rkolbi/voron2.4/DK-TAP-SENSORLESS-EBB36-CPAP-BEDFANS/ACTIVE/MACRO-PRINT_HANDLING.cfg

#.................................................................................................................
[gcode_macro _PRINT_VARIABLES]
variable_extruder_temp: 235
variable_extruder_temp2: 235
variable_extruder_warm: 160
variable_fpline: 37.5
variable_spline: 75.0   
variable_swap_executed: 0
variable_pause_on_layer_change: 0
gcode:
    M117 Happy Printing



#.................................................................................................................
[gcode_macro PRINT_START]
description: Performs all needed moves prior to printing
gcode:
    CLEAR_PAUSE                                            ; Clear pause state from previous print
    BED_MESH_CLEAR                                         ; Clear bed mesh data from the previous print
    M220 S100                                              ; Reset feedrate to 100%
    M221 S100                                              ; Reset flowrate to 100%
	
    # Bring in variables passed by the slicer. If needed variables are not passed then PRINT_START will use default values set in the printer.cfg file. 

    # SuperSlicer 'Start G-Code' example follows:
    # M104 S0 ; Stops PS/SS from sending temp waits separately
    # M140 S0
    # PRINT_START BED_TEMP=[first_layer_bed_temperature] EXTRUDER_TEMP=[first_layer_temperature] EXTRUDER_TEMP2=[temperature] CHAMBER_TEMP=[chamber_temperature] SOAK=15 PA=0.045 ST=0.21 SIZE={first_layer_print_min[0]}_{first_layer_print_min[1]}_{first_layer_print_max[0]}_{first_layer_print_max[1]}

    # PrusaSlicer 'Start G-Code' example follows (have to hard-write chamber temp):
    # M104 S0 ; Stops PS/SS from sending temp waits separately
    # M140 S0
    # PRINT_START BED_TEMP=[first_layer_bed_temperature] EXTRUDER_TEMP=[first_layer_temperature] EXTRUDER_TEMP2=[temperature] CHAMBER_TEMP=50 SOAK=15 PA=0.045 ST=0.21 SIZE={first_layer_print_min[0]}_{first_layer_print_min[1]}_{first_layer_print_max[0]}_{first_layer_print_max[1]}
    
    {% set FL_SIZE = params.SIZE|default("0_0_0_0")|string %}                                                               ; Get mesh parameters from slicer
    COMPUTE_MESH_PARAMETERS SIZE={FL_SIZE}                                                                                  ; Compute mesh parameters
    {% set PA = params.PA|default(printer.configfile.config['extruder']['pressure_advance'])|float %}                       ; Set pressure advance
    {% set ST = params.ST|default(printer.configfile.config['extruder']['pressure_advance_smooth_time'])|float %}           ; Set pressure advance
    {% set EXTRUDER_TEMP = params.EXTRUDER_TEMP|default(printer['gcode_macro globalvariables'].defaulttempnozzle)|float %}  ; Set first-layer extruder temperature
    {% set EXTRUDER_TEMP2 = params.EXTRUDER_TEMP2|default(EXTRUDER_TEMP)|float %}                                           ; Set extruder temperature
    {% set EXTRUDER_WARM = params.EXTRUDER_WARM|default(printer["gcode_macro globalvariables"].defaultwarmnozzle)|float %}  ; Set extruder warm temperature
    {% set SOAK = params.SOAK|default(printer["gcode_macro globalvariables"].preprintsoakminutes)|float %}                  ; Set pre-print soak time
    {% set BED_TEMP = params.BED_TEMP|default(printer["gcode_macro globalvariables"].defaulttempbed)|float %}               ; Set bed temperature
    {% set fpline = params.fpline|default(printer['gcode_macro globalvariables'].fpline)|float %}                           ; Get E value for first 120mm prime line, implemented as (fpline * NZLD)
    {% set spline = params.spline|default(printer['gcode_macro globalvariables'].spline)|float %}                           ; Get E value for second 120mm prime line, implemented as (spline * NZLD)
    {% set CHAMBER_TEMP = params.CHAMBER_TEMP|default(printer["gcode_macro globalvariables"].bedfanchambertemp)|float %}    ; Set chamber temperature
    SET_PRESSURE_ADVANCE ADVANCE={PA} SMOOTH_TIME={ST}                                                                      ; Set pressure advance
    SET_GCODE_VARIABLE MACRO=_PRINT_VARIABLES VARIABLE=extruder_temp VALUE={EXTRUDER_TEMP}                                  ; Set first-layer extruder temperature
    SET_GCODE_VARIABLE MACRO=_PRINT_VARIABLES VARIABLE=extruder_temp2 VALUE={EXTRUDER_TEMP2}                                ; Set extruder temperature
    SET_GCODE_VARIABLE MACRO=_PRINT_VARIABLES VARIABLE=extruder_warm VALUE={EXTRUDER_WARM}                                  ; Set extruder warm temperature
    SET_GCODE_VARIABLE MACRO=_PRINT_VARIABLES VARIABLE=swap_executed VALUE=0                                                ; Set swap flag to off
    SET_GCODE_VARIABLE MACRO=_PRINT_VARIABLES VARIABLE=pause_on_layer_change VALUE=0                                        ; Set layer change pause flag to off
    SET_GCODE_VARIABLE MACRO=_PRINT_VARIABLES VARIABLE=fpline VALUE={fpline}                                                ; Set first 120mm prime line, implemented as (fpline * NZLD)
    SET_GCODE_VARIABLE MACRO=_PRINT_VARIABLES VARIABLE=spline VALUE={spline}                                                ; Set second 120mm prime line, implemented as (spline * NZLD)
    SET_GCODE_VARIABLE MACRO=_BEDFANVARS VARIABLE=bedfanchambertarget VALUE={CHAMBER_TEMP}

    ; Override MACRO-BED_FANS variables with those from printer.cfg
    {% set bedfantripon = printer["gcode_macro globalvariables"].bedfantripon|float %}
    {% set bedfanmin = printer["gcode_macro globalvariables"].bedfanmin|float %}
    {% set bedfanmax = printer["gcode_macro globalvariables"].bedfanmax|float %}
    {% set bedfannormal = printer["gcode_macro globalvariables"].bedfannormal|float %}
    SET_GCODE_VARIABLE MACRO=_BEDFANVARS VARIABLE=bedfantripon VALUE={bedfantripon}
    SET_GCODE_VARIABLE MACRO=_BEDFANVARS VARIABLE=bedfanmin VALUE={bedfanmin}
    SET_GCODE_VARIABLE MACRO=_BEDFANVARS VARIABLE=bedfanmax VALUE={bedfanmax}
    SET_GCODE_VARIABLE MACRO=_BEDFANVARS VARIABLE=bedfannormal VALUE={bedfannormal}

    M118 {rawparams}                                       ; Display all passed parameters
    M118 gCode file passed the following to PRINT_START:   ; Display message on LCD screen

    M118 PA: {PA}
    M118 ST: {ST}
    M118 fpline: {fpline}
    M118 spline: {spline}
    M118 EXTRUDER, FIRST LAYER TEMP: {EXTRUDER_TEMP}
    M118 EXTRUDER, REST OF PRINT TEMP: {EXTRUDER_TEMP2}
    M118 EXTRUDER, WARM TEMP: {EXTRUDER_WARM}
    M118 SOAK: {SOAK}
    M118 BED TEMP: {BED_TEMP}
    M118 CHAMBER TEMP: {CHAMBER_TEMP}
    M118 Following parameters are set to prepare print:    ; Display message on LCD screen

    M140 S{BED_TEMP}                                       ; Set bed temperature
    G90                                                    ; Absolute positioning
    G21                                                    ; Millimeters
    M83                                                    ; Extruder relative mode
    G92 E0.0                                               ; Reset the extruder position
    SET_GCODE_OFFSET Z=0.0                                 ; Reset the G-Code Z offset
    M117 Performing initial homing.                        ; Display message on LCD screen
    BED_MESH_CLEAR                                         ; Clear bed mesh data from the previous print
    G28                                                    ; Home all axes
    M117 Performing initial QGL.                           ; Display message on LCD screen
    QUAD_GANTRY_LEVEL                                      ; Perform QGL
    G28 Z                                                  ; Home Z axis
    SET_HEATER_TEMPERATURE HEATER=extruder TARGET=0        ; Ensure hotend heater is off
    PARK_Center                                            ; Park the nozzle at the center of the bed
    M117 Bringing bed to temperature.                      ; Display message on LCD screen
    STATUS_HEATING                                         ; Set status to heating
    SET_NOZZLE_LEDS_ON                                     ; Turn on nozzle LEDs

    M190 S{BED_TEMP}                                       ; Wait for the bed to reach temperature

    {% if params.NONPRINT %}                               ; If NONPRINT is passed then need to use the blocking wait routine
        _HEAT_WAIT MINUTES={SOAK}                          ; Wait for SOAK minutes
        _PRINT_START2                                      ; Start sudo print
      {% else %}                                           ; If NONPRINT is not passed then continue and use the non-blocking wait routine
        _WAIT_Start MINUTES={SOAK}                         ; Wait for SOAK minutes
    {% endif %}                                            ; End if statement


#.................................................................................................................
[gcode_macro _PRINT_START2]
description: Part 2 - Performs all needed moves prior to printing
gcode:
    RESUME_BASE                                            ; Resume print
    {% set EXTRUDER_WARM = printer["gcode_macro _PRINT_VARIABLES"].extruder_warm|int %}   ; Get extruder warm temperature
    {% set EXTRUDER_TEMP = printer["gcode_macro _PRINT_VARIABLES"].extruder_temp|int %}   ; Get first-layer extruder temperature
    {% set EXTRUDER_TEMP2 = printer["gcode_macro _PRINT_VARIABLES"].extruder_temp2|int %} ; Get extruder temperature
    M104 S{EXTRUDER_WARM}                                  ; Set extruder temperature
    M117 Warming nozzle for hot level.                     ; Display message on LCD screen
    TEMPERATURE_WAIT SENSOR=extruder MINIMUM={EXTRUDER_WARM} MAXIMUM={EXTRUDER_WARM + 3}  ; Wait for extruder warm temp within 3 degrees
    CURRENT_HIGH                                           ; Set current to high
    M117 Performing hot level.                             ; Display message on LCD screen
    M400                                                   ; Wait for moves to complete
    G3201                                                  ; Perform hot level and mesh
    M104 S{EXTRUDER_TEMP}                                  ; Set first-layer extruder temperature
    M117 Moving nozzle to purgle line start position.      ; Display message on LCD screen
    G1 X0 Y20 F4000                                        ; Move nozzle to side
    G1 Z1.5                                                ; Move nozzle to over bed
    M400                                                   ; Wait for moves to finish
    STATUS_HEATING                                         ; Set status to heating
    SET_NOZZLE_LEDS_ON                                     ; Turn on nozzle LEDs
    M117 Bringing nozzle to temperature.                   ; Display message on LCD screen
    M118 Bringing nozzle to temperature.                   ; Display message on LCD screen
    TEMPERATURE_WAIT SENSOR=extruder MINIMUM={EXTRUDER_TEMP} MAXIMUM={EXTRUDER_TEMP + 3}  ; Wait for extruder temp within 3 degrees
    _FILAMENT_READY                                        ; Perform filament purge line and readies for print
    M117 Printing.                                         ; Display message on LCD screen
    M118 Printing.                                         ; Display message on LCD screen
    STATUS_PRINTING                                        ; Set status to printing
    M400
    SET_NOZZLE_LEDS_ON                                     ; Turn on nozzle LEDs


#.................................................................................................................	
[gcode_macro _FILAMENT_READY]
description: Performs filament specific purge line and readies for print
gcode:
    STATUS_BUSY                                            ; Set status to busy
    SET_NOZZLE_LEDS_ON                                     ; Turn on nozzle LEDs
    SET_VELOCITY_LIMIT ACCEL={printer["gcode_macro globalvariables"].limitaccel|float} ACCEL_TO_DECEL={printer["gcode_macro globalvariables"].limitdecel|float} ; Set velocity limits
    {% set NZLD = printer.configfile.config["extruder"]["nozzle_diameter"]|float %}                                                                             ; Get nozzle diameter from config
    {% set purgeRetract = printer["gcode_macro globalvariables"].purgeretract|float %}                                                                          ; Get retraction for purge line from config
    {% set X_MeshCenter, Y_MeshCenter = printer["gcode_macro _ADAPTIVE_MESH_VARIABLES"].mesh_center.split(',')|map('trim')|map('int') %}                        ; Get mesh center
    {% set EXTRUDER_TEMP = printer["gcode_macro _PRINT_VARIABLES"].extruder_temp|int %}                                                                         ; Get first-layer extruder temperature
    {% set EXTRUDER_TEMP2 = printer["gcode_macro _PRINT_VARIABLES"].extruder_temp2|int %}                                                                       ; Get extruder temperature
    {% set fpline = printer["gcode_macro _PRINT_VARIABLES"].fpline|float %}                                                                                     ; Get E value for first 120mm prime line
    {% set spline = printer["gcode_macro _PRINT_VARIABLES"].spline|float %}                                                                                     ; Get E value for second 120mm prime line

    {% set E20 = ( (0.1147475 * NZLD) * 20) |float %}      ; Calculate E value for 20mm line
    {% set E40 = ( (0.1147475 * NZLD) * 40) |float %}      ; Calculate E value for 40mm line

    M117 Purging nozzle.                                   ; Display message on LCD screen
    G1 X0 Y19.8 Z3 F300.0                                  ; Move nozzle
    M400                                                   ; Wait for moves to complete
    G1 X130 Y4.0 Z0.3 F3000.0                              ; Move nozzle to start position
    G1 X010 Y4.0 Z0.3 F1500.0 E{(fpline * NZLD)}           ; Extrude filament
    G1 X010 Y4.3 Z0.3 F5000.0                              ; Move nozzle
    M104 S{EXTRUDER_TEMP2}                                 ; Set extruder temperature
    G1 X130 Y4.3 Z0.3 F1500.0 E{(spline * NZLD)}           ; Extrude filament
    M400                                                   ; Wait for moves to complete

        ; Pressure advance verification line check
        M117 Printing PA test line at {EXTRUDER_TEMP2}C    ; Display message on LCD screen
        G1 Z0.25 F300                                      ; Move to layer height
        G1 X150 Y4.3 E{E20} F300                           ; Print line part one
        G1 X190 Y4.3 E{E40} F9000                          ; Print line part two
        G1 X210 Y4.3 E{E20} F300                           ; Print line part three
        M400                                               ; Wait for moves to complete
        ; End of Pressure advance verification line check

    M117 Increasing extruder to {EXTRUDER_TEMP}C for 1st layer  ; Display message on LCD screen
    M104 S{EXTRUDER_TEMP}                                  ; Set for first-layer extruder temperature
                                                           ; Can swap M104 with M109 to wait for temperature if hotend is slower
    G1 E-{purgeRetract} F3000                              ; Retract filament   
    G92 E0.0                                               ; Reset the extruder position
    G1 Z3 F3000                                            ; Move nozzle up
    M400                                                   ; Wait for moves to complete
    G1 X{X_MeshCenter} Y{Y_MeshCenter} F4000               ; Move nozzle to center of mesh
    G92 E0                                                 ; Reset extruder position
    M400                                                   ; Wait for moves to complete



#.................................................................................................................
[gcode_macro PRINT_END]
description: Performs all needed actions upon completion of printing
gcode:
    {% set EndRetract = printer["gcode_macro globalvariables"].endretract|float %}                                                              ; Get end of print retraction distance
    {% set EXTRUDER_WARM = printer["gcode_macro _PRINT_VARIABLES"].extruder_warm|int %}                                                         ; Get warm nozzle temperature
    SET_VELOCITY_LIMIT ACCEL={printer["gcode_macro globalvariables"].nplimitaccel|float} ACCEL_TO_DECEL={printer["gcode_macro globalvariables"].nplimitdecel|float} ; Set velocity limits
    SET_GCODE_VARIABLE MACRO=_ADAPTIVE_MESH_VARIABLES VARIABLE=mesh_center VALUE='"0,0"'                                                        ; Reset mesh center
    SET_GCODE_VARIABLE MACRO=_PRINT_VARIABLES VARIABLE=extruder_temp VALUE={printer["gcode_macro globalvariables"].defaulttempnozzle|float}     ; Reset extruder temperature
    SET_GCODE_VARIABLE MACRO=_PRINT_VARIABLES VARIABLE=extruder_warm VALUE={printer["gcode_macro globalvariables"].defaultwarmnozzle|float}     ; Reset warm nozzle temperature
    SET_GCODE_VARIABLE MACRO=_PRINT_VARIABLES VARIABLE=swap_executed VALUE=0                                                                    ; Set swap flag to off

    G91                                                    ; Relative positioning
    G0 Z5 F1000                                            ; Raise Z by 5mm
    G90                                                    ; Absolute positioning
    M220 S100                                              ; Reset speed to 100%
    M221 S100                                              ; Reset flow to 100%
    G92 E0                                                 ; Reset the extruder position
    G1 E-{EndRetract} F3600                                ; Retract filament
    M400                                                   ; Wait for moves to complete
    SAVE_GCODE_STATE NAME=STATE_PRINT_END                  ; Save current state   
    M400                                                   ; Wait for moves to complete
    BEDFANSOFF                                             ; Turn off bed fans
    TURN_OFF_HEATERS                                       ; Turn off heaters
    CURRENT_NORMAL                                         ; Set current to normal
    _COOL_WAIT MINUTES={printer["gcode_macro globalvariables"].postprintcool|float} NZL_TEMP={EXTRUDER_WARM} ; Wait for cool minutes
    PARK_UpperRight                                        ; Park the nozzle at the upper right of the bed
    M18 X Y E                                              ; Disable all steppers
    BED_MESH_CLEAR                                         ; Clear bed mesh data from the previous print
    RESTORE_GCODE_STATE NAME=STATE_PRINT_END               ; Restore saved state
    _COOL_WAIT MINUTES={printer["gcode_macro globalvariables"].postprintparkcool|float} NZL_TEMP=80 ; Wait for cool minutes until NZL 80c

    STOP_LED_EFFECTS                                       ; Turn off LED effects
    SET_LED LED=sb_leds RED=.3 GREEN=.5 BLUE=.4            ; Set LED to green
    M117 Finished printing, check nozzle clear.            ; Display message on LCD screen
    M118 Finished printing, check nozzle clear.            ; Display message on the terminal



#.................................................................................................................
[gcode_macro CANCEL_PRINT]
description: Cancel the actual running print
rename_existing: CANCEL_PRINT_BASE
gcode:
    {% if printer["gcode_macro _WAIT_Variable"].waiting %}          ; If waiting for user input
        WAIT_Quit                                                   ; Quit waiting
    {% else %}
    {% set EndRetract = printer["gcode_macro globalvariables"].endretract|float %}                                                              ; Get end of print retraction distance
    SET_VELOCITY_LIMIT ACCEL={printer["gcode_macro globalvariables"].nplimitaccel|float} ACCEL_TO_DECEL={printer["gcode_macro globalvariables"].nplimitdecel|float} ; Set velocity limits
    SET_GCODE_VARIABLE MACRO=_ADAPTIVE_MESH_VARIABLES VARIABLE=mesh_center VALUE='"0,0"'                                                        ; Reset mesh center
    SET_GCODE_VARIABLE MACRO=_PRINT_VARIABLES VARIABLE=extruder_temp VALUE={printer["gcode_macro globalvariables"].defaulttempnozzle|float}     ; Reset extruder temperature
    SET_GCODE_VARIABLE MACRO=_PRINT_VARIABLES VARIABLE=extruder_warm VALUE={printer["gcode_macro globalvariables"].defaultwarmnozzle|float}     ; Reset warm nozzle temperature
    SET_GCODE_VARIABLE MACRO=_PRINT_VARIABLES VARIABLE=swap_executed VALUE=0                                                                    ; Set swap flag to off
    SAVE_GCODE_STATE NAME=STATE_PRINT_END                  ; Save current state
    M400                                                   ; Wait for moves to complete
    M220 S100                                              ; Reset speed to 100%
    M221 S100                                              ; Reset flow to 100%
    G92 E0                                                 ; Reset the extruder position
    {% if printer.extruder.can_extrude|lower == 'true' %}  ; If extruder can extrude
        G1 E-{EndRetract} F3600                            ; Retract filament
    {% endif %}                                            ; End if extruder check
    CLEAR_PAUSE                                            ; Clear pause state
    BEDFANSOFF                                             ; Turn off bed fans
    TURN_OFF_HEATERS                                       ; Turn off heaters
    CANCEL_PRINT_BASE                                      ; Call original macro
    CURRENT_NORMAL                                         ; Set current to normal
    M106 S250                                              ; Turn on the fan
    G90                                                    ; Absolute positioning
    PARK_UpperRight                                        ; Park the nozzle at the upper right of the bed
    M18 X Y E                                              ; Disable all steppers
    BED_MESH_CLEAR                                         ; Clear bed mesh data from the previous print
    RESTORE_GCODE_STATE NAME=STATE_PRINT_END               ; Restore saved state
    _COOL_WAIT MINUTES={printer["gcode_macro globalvariables"].postprintparkcool|float} NZL_TEMP=80 ; Wait for cool minutes until NZL 80c

    M117 Cancelled print, check nozzle clear.              ; Display message on LCD screen
    M118 Cancelled print, check nozzle clear.              ; Display message on the terminal
    STATUS_READY                                           ; Set status to ready
    {% endif %} 


#.................................................................................................................
[gcode_macro PAUSE]
description: Pause the actual running print
rename_existing: PAUSE_BASE
gcode:
    {% set X_MID = printer.configfile.config["stepper_x"]["position_max"]|float / 2.0 %} ; Get X midpoint
    SET_GCODE_VARIABLE MACRO=_PRINT_VARIABLES VARIABLE=extruder_temp VALUE="{printer[printer.toolhead.extruder].target}"  ; Save current extruder temperature
    {% set x = params.X|default(X_MID) %}                   ; X position to move to
    {% set y = params.Y|default(20) %}                      ; Y position to move to
    {% set z = params.Z|default(10)|float %}                ; Z position to move to
    {% set e = params.E|default(1) %}                       ; E position to move to
    {% set max_z = printer.toolhead.axis_maximum.z|float %} ; Maximum Z position
    {% set act_z = printer.toolhead.position.z|float %}     ; Actual Z position
    {% set lift_z = z|abs %}                                ; Z lift distance
    {% if act_z < (max_z - lift_z) %}                       ; Check if Z is high enough
        {% set z_safe = lift_z %}                           ; Set Z lift distance
      {% else %}                                            ; If not high enough
        {% set z_safe = max_z - act_z %}                    ; Set Z lift distance to maximum
    {% endif %}                                             ; End if Z is high enough
    PAUSE_BASE                                              ; Call original macro
    G91                                                     ; Relative positioning
    {% if printer.extruder.can_extrude|lower == 'true' %}   ; If extruder can extrude
        G1 E-{e} F2100                                      ; Retract filament
      {% else %}                                            ; If extruder can't extrude
        {action_respond_info("Extruder not hot enough")}    ; Display message on terminal
    {% endif %}                                             ; End if extruder can extrude
    {% if "xyz" in printer.toolhead.homed_axes %}           ; If printer is homed
        G1 Z{z_safe}                                        ; Lift Z
        G90                                                 ; Absolute positioning
        G1 X{x} Y{y} F4000                                  ; Move to X Y
      {% else %}                                            ; If printer is not homed
        {action_respond_info("Printer not homed")}          ; Display message on terminal
    {% endif %}                                             ; End if printer is homed



#.................................................................................................................
[gcode_macro M600]
description: Call to pause
gcode:
    SET_GCODE_VARIABLE MACRO=_PRINT_VARIABLES VARIABLE=extruder_temp VALUE="{printer[printer.toolhead.extruder].target}"  ; Save current extruder temperature
    SAVE_GCODE_STATE NAME=M600_state                      ; Save current state
    SET_GCODE_VARIABLE MACRO=_PRINT_VARIABLES VARIABLE=swap_executed VALUE=1  ; Set swap flag to on
    RESPOND TYPE=error MSG="ALERT: M600 Called!"          ; Respond with error
    SET_IDLE_TIMEOUT TIMEOUT=6000                         ; Extend timeout while waiting for swap
    PAUSE_BASE                                            ; Pause print
    STATUS_ATTENTION                                      ; Flash LEDs to get attention
    {% set X_MID = printer.configfile.config["stepper_x"]["position_max"]|float / 2.0 %}  ; Get X midpoint
    G91                                                   ; Relative positioning
    G1 E-5 F4000                                          ; Retract 5mm
    G1 Z+10                                               ; Raise Z by 10mm
    G90                                                   ; Return to Absolute positioning
    G0 X{X_MID} Y20 F3000                                 ; Move to an area where can easily load filament 
    G92 E0                                                ; Reset the extruder position to 0



#.................................................................................................................
[gcode_macro _LAYER_CHANGE]
description: Check if to pause once layer change occurs
gcode:
    # This macro is for use by the slicer's output; it is not meant to be executed by the user directly.
    # `_LAYER_CHANGE LAYER={layer_num}` has to be in your slicer's gcode block `After Layer Change`
    {% set LAYER = params.LAYER|default(0)|int	%}                                                ; Grab current layer from slicer output
    {% if printer["gcode_macro _PRINT_VARIABLES"].pause_on_layer_change > 0 %}                    ; Determine if pause on layer change is on
        {% if printer["gcode_macro _PRINT_VARIABLES"].pause_on_layer_change == 1 %}               ; If pause_on_layer_change is set to 1, pause on next layer change
            SET_GCODE_VARIABLE MACRO=_PRINT_VARIABLES VARIABLE=pause_on_layer_change VALUE=0      ; Since we are pausing, set the flag to 0 to reset pause on the next layer
            M118 PAUSING NOW, current layer {LAYER}.
            M118 Executing M600/PAUSE.
            M600
        {% else %}
            {% if printer["gcode_macro _PRINT_VARIABLES"].pause_on_layer_change == LAYER %}       ; If pause_on_layer_change is not 0 or 1, pause on the specified layer change
                SET_GCODE_VARIABLE MACRO=_PRINT_VARIABLES VARIABLE=pause_on_layer_change VALUE=0  ; Since we are pausing, set the flag to 0 to reset pause on the next layer
                M118 PAUSING NOW, the designated layer was {LAYER}.
                M118 Executing M600/PAUSE.
                M600
            {% endif %}
        {% endif %}
    {% endif %}

#.................................................................................................................
[gcode_macro LC_PAUSE]
description: Set to pause once layer change occurs
gcode:
    # LC_PAUSE will toggle on/off the pause on the next layer flag. If no LAYER is passed, the flag will be set to 
    # pause on the next layer change. If a LAYER is passed, a pause on layer change will occur when the slicer's passed
    # layer value (_LAYER_CHANGE LAYER={layer_num}) is equal to the user's LAYER passed with this macro.

    {% set LAYER = params.LAYER|default(1)|int	%}                                             ; Grab the LAYER value passed by the user
    {% if printer["gcode_macro _PRINT_VARIABLES"].pause_on_layer_change > 0 %}                 ; If Pause on the next layer is active, toggle it off
        SET_GCODE_VARIABLE MACRO=_PRINT_VARIABLES VARIABLE=pause_on_layer_change VALUE=0
        M118 Layer Change Pause is now set to OFF.
    {% else %}
        SET_GCODE_VARIABLE MACRO=_PRINT_VARIABLES VARIABLE=pause_on_layer_change VALUE={LAYER} ; Since Pause on the next layer is not active, toggle it on
        M118 Layer Change Pause is now set to ON.
            {% if LAYER == 1 %}                                                                ; If no LAYER value was passed by the user, pause on the next layer change
                M118 PAUSE will occur upon the next layer change.
            {% else %}
                M118 PAUSE will occur upon change to layer {LAYER}.                            ; If the LAYER value was passed by the user, set the flag to that number to pause at
           {% endif %}
    {% endif %}



#.................................................................................................................
[gcode_macro RESUME]
description: Resume the actual running print
rename_existing: RESUME_BASE
gcode:
    {% if printer["gcode_macro _WAIT_Variable"].waiting %}          ; If waiting for user input
        WAIT_Quit                                                   ; Quit waiting
      {% else %}                                                    ; If not waiting for user input
        {% set EXTRUDER_TEMP = printer["gcode_macro _PRINT_VARIABLES"].extruder_temp|int %} ; Get extruder temperature
        {% set e = params.E|default(1) %}                           ; Edit to your retract length
        {% if 'VELOCITY' in params|upper %}                         ; If VELOCITY is set in the macro call
            {% set get_params = ('VELOCITY=' + params.VELOCITY)  %} ; set get_params to the VELOCITY value
          {%else %}                                                 ; If VELOCITY is not set in the macro call
            {% set get_params = "" %}                               ; Set get_params to nothing
        {% endif %}                                                 ; End if VELOCITY is set in the macro call
        G91                                                         ; Relative positioning
        {% if printer.extruder.can_extrude|lower == 'true' %}       ; If extruder can extrude
            G1 E{e} F2100                                           ; Retract filament
          {% else %}                                                ; If extruder cannot extrude
            M117 Bringing nozzle to {EXTRUDER_TEMP}C.               ; Display message on LCD screen
            M109 S{EXTRUDER_TEMP}                                   ; Wait for the nozzle to reach temperature
            G1 E{e} F21                                             ; Retract filament
        {% endif %}                                                 ; End if extruder can extrude
        {% if printer["gcode_macro _PRINT_VARIABLES"].swap_executed == 1%}  ; If M600 was called, return to that saved state
            RESTORE_GCODE_STATE NAME=M600_state                     ; Restore saved state from M600
            M400                                                    ; Wait for moves to complete
            STATUS_PRINTING                                         ; Set status to printing
            SET_NOZZLE_LEDS_ON                                      ; Turn on nozzle LEDs
            RESUME_BASE {get_params}                                ; Call original macro
            SET_IDLE_TIMEOUT TIMEOUT=600                            ; Return timeout to normal
            SET_GCODE_VARIABLE MACRO=_PRINT_VARIABLES VARIABLE=swap_executed VALUE=0  ; Set swap flag to off
        {% else %}
            STATUS_PRINTING                                         ; Set status to printing
            SET_NOZZLE_LEDS_ON                                      ; Turn on nozzle LEDs
            RESUME_BASE {get_params}                                ; Call original macro
        {% endif %}  
    {% endif %}                                                     ; End if waiting for user input
