rkolbi/voron2.4/Tap-Tap-Sensorless-Huvud-BedFans/ACTIVE/CONFIG-BED_FANS.cfg

# Modified version of https://github.com/VoronDesign/VoronUsers/tree/master/printer_mods/Ellis/Bed_Fans

[gcode_macro _BEDFANVARS]
variable_fansenclosuretarget: 45                                                                      ; Enclosure temp to switch to medium speed fans
variable_fansenclosurereachedtemp: 0                                                                  ; Flag to indicate enclosure temp has reached target


[gcode_macro BEDFANSSLOW]
gcode:
    SET_FAN_SPEED FAN=BedInner SPEED={ printer["gcode_macro globalvariables"].fansinnerslow|float }   ; Set inner bed fans to slow speed
    SET_FAN_SPEED FAN=BedOuter SPEED={ printer["gcode_macro globalvariables"].fansouterslow|float }   ; Set outer bed fans to slow speed

[gcode_macro BEDFANSMEDIUM]
gcode:
    SET_FAN_SPEED FAN=BedInner SPEED={ printer["gcode_macro globalvariables"].fansinnermedium|float } ; Set inner bed fans to medium speed
    SET_FAN_SPEED FAN=BedOuter SPEED={ printer["gcode_macro globalvariables"].fansoutermedium|float } ; Set outer bed fans to medium speed

[gcode_macro BEDFANSFAST]
gcode:
    SET_FAN_SPEED FAN=BedInner SPEED={ printer["gcode_macro globalvariables"].fansinnerfast|float }   ; Set inner bed fans to fast speed
    SET_FAN_SPEED FAN=BedOuter SPEED={ printer["gcode_macro globalvariables"].fansouterfast|float }   ; Set outer bed fans to fast speed

[gcode_macro BEDFANSOFF]
gcode:
    SET_FAN_SPEED FAN=BedInner SPEED=0                                                                ; Turn off inner bed fans
    SET_FAN_SPEED FAN=BedOuter SPEED=0                                                                ; Turn off outer bed fans
    UPDATE_DELAYED_GCODE ID=bedfanloop DURATION=0                                                     ; Cancel bed fan loop if it's running

[gcode_macro TURN_OFF_HEATERS]
rename_existing: _TURN_OFF_HEATERS
gcode:
    BEDFANSOFF                                                                                        ; Turn off bed fans
    _TURN_OFF_HEATERS                                                                                 ; Turn off heaters



[gcode_macro SET_HEATER_TEMPERATURE]
rename_existing: _SET_HEATER_TEMPERATURE
gcode:
    {% set HEATER = params.HEATER|default("None") %}                                                  ; Heater to set temperature for
    {% set TARGET = params.TARGET|default(0)|int %}                                                   ; Target temperature
    {% set fansbedtempthreshold = printer["gcode_macro globalvariables"].fansbedtempthreshold|int %}  ; Bed temp threshold for bed fans 

    {% if HEATER|lower == "heater_bed" %}                                                             ; If heater is bed
        M99140 S{ TARGET }                                                                            ; Set bed temperature
    {% else %}                                                                                        ; If heater is not bed
        _SET_HEATER_TEMPERATURE {rawparams}                                                           ; Set heater temperature
    {% endif %}                                                                                       ; End if heater is bed

    {% if HEATER|lower == "heater_bed" %}                                                             ; If heater is bed
        {% if TARGET >= fansbedtempthreshold %}                                                       ; If the bed's target temp is above the bed fan trip threshold
            BEDFANSSLOW                                                                               ; Set bed fans to slow speed as bed is heating
            UPDATE_DELAYED_GCODE ID=bedfanloop DURATION=1                                             ; Start bed fan loop
        {% else %}                                                                                    ; If the bed's target temp is below the bed fan trip threshold
            BEDFANSOFF                                                                                ; Turn off bed fans
            UPDATE_DELAYED_GCODE ID=bedfanloop DURATION=0                                             ; Cancel bed fan loop if it's running
        {% endif %}                                                                                   ; End if the bed's target temp is above the bed fan trip threshold
    {% endif %}                                                                                       ; End if heater is bed



[gcode_macro M190]
rename_existing: M99190
gcode:
    {% set S = params.S|int %}                                                                        ; Bed target temperature
    {% set fansbedtempthreshold = printer["gcode_macro globalvariables"].fansbedtempthreshold|int %}  ; Grab the bed fan trip threshold

    {% if S >= fansbedtempthreshold %}                                                                ; If the bed target temp is above the bed fan trip threshold
        BEDFANSSLOW                                                                                   ; Set bed fans to low speed fans while the bed is heating
    {% else %}                                                                                        ; If the bed target temp is below the bed fan trip threshold
        BEDFANSOFF                                                                                    ; Turn off bed fans
    {% endif %}                                                                                       ; End if the bed target temp is above the bed fan trip threshold

    M140 {% for p in params %}{'%s%s' % (p, params[p])}{% endfor %}                                   ; Set bed target temp
  
    {% if S != 0 %}                                                                                   ; If the bed target temp is not 0
        TEMPERATURE_WAIT SENSOR=heater_bed MINIMUM={ S|int } MAXIMUM={ S|int + 5 }                    ; Wait for bed temp within 5 degrees
    {% endif %}                                                                                       ; End if bed target temp is not 0

    {% if S >= fansbedtempthreshold %}                                                                ; Now that bed is at temperature, If the bed target temp is above the bed fan trip threshold
        BEDFANSFAST                                                                                   ; Set bed fans to fast speed
    {% endif %}                                                                                       ; End if the bed target temp is above the bed fan trip threshold



[gcode_macro M140]
rename_existing: M99140
gcode:
	{% set S = params.S|float %}                                                                      ; Bed target temperature
	SET_HEATER_TEMPERATURE HEATER=heater_bed TARGET={S}                                               ; Set bed target temp



[delayed_gcode bedfanloop]
gcode:
    {% set fansbedtempthreshold = printer["gcode_macro globalvariables"].fansbedtempthreshold|int %}  ; Grab the bed fan trip threshold
    {% set fansenclosuretarget = printer["gcode_macro _BEDFANVARS"].fansenclosuretarget|int %}        ; Get the enclosure target temp
    {% set enclosure_temp = printer["temperature_sensor enclosure"].temperature|float %}              ; Get the enclosure temp
    {% set enclosurereachedtemp = printer["gcode_macro _BEDFANVARS"].fansenclosurereachedtemp|int %}  ; Get the enclosure reached temperature flag

    {% if printer.heater_bed.target >= fansbedtempthreshold %}                                        ; If the bed target temp is above the bed fan trip threshold
        {% if printer.heater_bed.temperature|int >= (printer.heater_bed.target|int - 1) %}            ; If the bed temp is within 1 degree of the target temperature
            {% if enclosure_temp < fansenclosuretarget %}                                             ; If the enclosure temp is below the enclosure target temp
                BEDFANSFAST                                                                           ; Set bed fans to fast speed
            {% else %}                                                                                ; If the enclosure temp is above the enclosure target temp
                BEDFANSMEDIUM                                                                         ; Set bed fans to medium speed
                {% if enclosurereachedtemp == 0 %}                                                    ; If the enclosure reached temperature flag is 0
                    SET_GCODE_VARIABLE MACRO=_BEDFANVARS VARIABLE=fansenclosurereachedtemp VALUE=1    ; Set the enclosure reached temperature flag to 1
                {% endif %}                                                                           ; End if the enclosure reached temperature flag is 0
            {% endif %}                                                                               ; End if the enclosure temp is below the enclosure target temp
        {% else %}                                                                                    ; If the bed temp is not within 1 degree of the target temperature
            BEDFANSSLOW                                                                               ; Set bed fans to slow speed
        {% endif %}                                                                                   ; End if the bed temp is within 1 degree of the target temperature
        UPDATE_DELAYED_GCODE ID=bedfanloop DURATION=5                                                 ; Restart bed fan loop
    {% endif %}                                                                                       ; End if the bed target temp is above the bed fan trip threshold

    {% if enclosurereachedtemp == 1 %}                                                                ; If the enclosure reached temperature flag is 1
        SET_GCODE_VARIABLE MACRO=_BEDFANVARS VARIABLE=fansenclosurereachedtemp VALUE=2                ; Set the enclosure reached temperature flag to 2
        WAIT_Quit                                                                                     ; Stop the pre-print wait cycle and get the print going
    {% endif %}                                                                                       ; End if the enclosure reached temperature flag is 1
