rkolbi/voron2.4/DK-TAP-SENSORLESS-EBB36-CPAP-BEDFANS/ACTIVE/MACRO-HOMING_LEVELING.cfg

#.................................................................................................................
[homing_override]
axes: xyz
gcode:
    STATUS_HOMING                                                                             ; Set status to homing
    SET_NOZZLE_LEDS_ON                                                                        ; Turn on nozzle LEDs
    {% set X_MID = printer.configfile.config["stepper_x"]["position_max"]|float / 2.0 %}      ; Get X midpoint
    {% set Y_MID = printer.configfile.config["stepper_y"]["position_max"]|float / 2.0 %}      ; Get Y midpoint
    {% set MeshCenter = printer["gcode_macro _ADAPTIVE_MESH_VARIABLES"].mesh_center|string %} ; Get mesh center
    {% set X_MeshCenter, Y_MeshCenter = MeshCenter.split(',')|map('trim')|map('int') %}       ; Split mesh center into X and Y
    {% set Home_ALL = 'X' not in params and 'Y' not in params and 'Z' not in params %}        ; Check if all axes are being homed
    {% set Z_POS = printer.toolhead.position.z %}                                             ; Get current Z position

    # If Z-axis is not homed, a full homed sequence will be run. Comment out the 'Safety On' line below if this is not desired.
    {% if "z" not in printer.toolhead.homed_axes %}        ; Check if Z not already homed
        {% set Home_ALL = 'Safety On' %}                   ; ! THIS WILL HOME ALL AXIS IF Z IS NOT HOMED, COMMENT OUT IF THIS IS NOT DESIRED !
        SET_KINEMATIC_POSITION Z=0                         ; Reset Z position to 0
        G0 Z10 F3600                                       ; Raise toolhead 10mm since unknown/not homed
        M18 Z                                              ; Disable Z stepper to ensure a false-homed status is not set
      {% else %}                                           ; IF Z is already homed
        {% if Z_POS < 10 %}                                ; Check if Z is below 10mm
            G90                                            ; Absolute positioning
            G0 Z10                                         ; If Z was below 10mm, raise it to 10mm for safety
          {% else %}                                       ; IF Z is already above 10mm
            G91                                            ; Relative positioning
            G0 Z1 F3600                                    ; If Z was above 10mm, raise by 1mm for safety
            G90                                            ; Absolute positioning
        {% endif %}                                        ; End Z position check
    {% endif %}                                            ; End Z homed check

    {% if Home_ALL or 'X' in params %}                     ; If 'Home_ALL' is set, or 'X' is in params, then home X
        G28 X                                              ; Home X
    {% endif %}                                            ; End X homing check

    {% if Home_ALL or 'Y' in params %}                     ; If 'Home_ALL' is set, or 'Y' is in params, then home Y
        G28 Y                                              ; Home Y
    {% endif %}                                            ; End Y homing check
  
    {% if Home_ALL or 'Z' in params %}                     ; If 'Home_ALL' is set, or 'Z' is in params, then home Z
        G90                                                ; Absolute positioning
        {% if X_MeshCenter > 0 and Y_MeshCenter > 0 %}     ; If mesh center is set, use it
            G0 X{X_MeshCenter} Y{Y_MeshCenter} F4000       ; Move to mesh center    
          {% else %}                                       ; If the mesh center is not set, use the printer's center
            G0 X{X_MID} Y{Y_MID} F4000                     ; Move to printer center
        {% endif %}                                        ; End mesh center check
        G28 Z                                              ; Home Z
        G1 Z10 F3600                                       ; Raise toolhead 10mm
    {% endif %}                                            ; End Z homing check

    STATUS_READY                                           ; Set status to ready
    SET_NOZZLE_LEDS_ON                                     ; Turn on nozzle LEDs	


#.................................................................................................................
[gcode_macro G32]
gcode:
    BED_MESH_CLEAR                                         ; Clear bed-mesh
    G28                                                    ; Home
    M400                                                   ; Wait for moves to finish
    QUAD_GANTRY_LEVEL                                      ; Quad gantry level
    M400                                                   ; Wait for moves to finish
    G28 Z                                                  ; Home Z
    M400                                                   ; Wait for moves to finish



#.................................................................................................................
[gcode_macro QUAD_GANTRY_LEVEL]
rename_existing: QUAD_GANTRY_LEVEL_ORIGINAL
description: Levels the four Z-axis gantry corners
gcode:
    {% if printer.toolhead.homed_axes != "xyz" %}          ; Home if not already homed
        G28                                                ; Home
        M400                                               ; Wait for moves to finish
    {% endif %}                                            ; End homing check
    STATUS_LEVELING                                        ; Set status to leveling
    SET_NOZZLE_LEDS_ON                                     ; Turn on nozzle LEDs
    QUAD_GANTRY_LEVEL_ORIGINAL                             ; Run original macro
    STATUS_READY                                           ; Set status to ready
    SET_NOZZLE_LEDS_ON                                     ; Turn on nozzle LEDs



#.................................................................................................................
[gcode_macro G3201]
description: Clears bed-mesh and performs G28, QGL, G28-Z, and applies bed-mesh
gcode:
    BED_MESH_CLEAR                                         ; Clear bed-mesh
    G28                                                    ; Home
    M400                                                   ; Wait for moves to finish
    QUAD_GANTRY_LEVEL_ORIGINAL                             ; Quad gantry level
    M400                                                   ; Wait for moves to finish
    G0 Z10 F3600                                           ; Raise toolhead 10mm
    M400                                                   ; Wait for moves to finish
    G28 Z                                                  ; Home Z
    M400                                                   ; Wait for moves to finish
    ADAPTIVE_BED_MESH                                      ; Run adaptive bed-mesh
    M400                                                   ; Wait for moves to finish
    STATUS_READY                                           ; Set status to ready
    SET_NOZZLE_LEDS_ON                                     ; Turn on nozzle LEDs
